fibonacid/foss-dj-player/design/brand/exports/fdjp/fdjp_dark_3xl.png

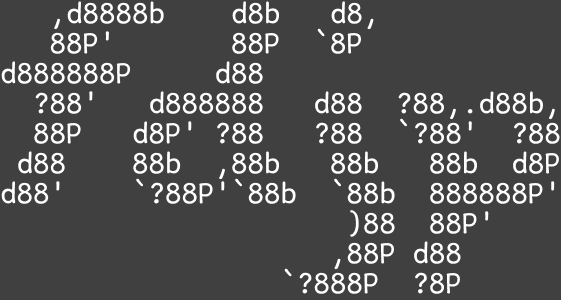
design/brand/exports/fdjp/fdjp_dark_3xl.png
