fibonacid/foss-dj-player/design/brand/exports/fdjp/fdjp_light_3xl.png

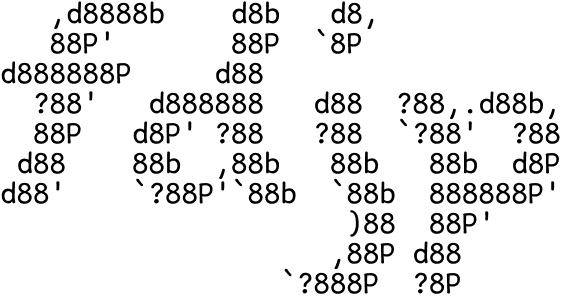
design/brand/exports/fdjp/fdjp_light_3xl.png
